AlexGyver/NixieClock_v2/case/IN-12_Max/Кнопки3.png

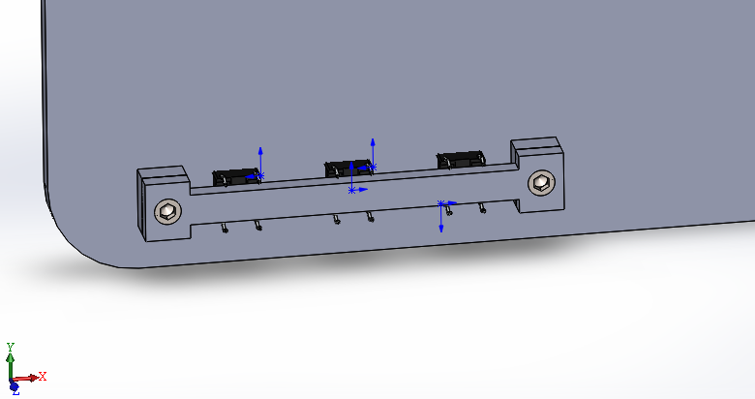
case/IN-12_Max/Кнопки3.png
