AlexGyver/NixieClock_v2/case/IN-12_Max/Крышка.png

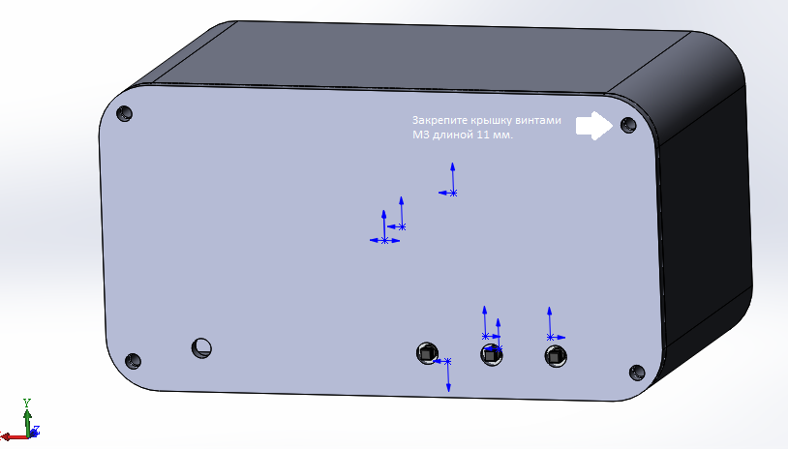
case/IN-12_Max/Крышка.png
