AlexGyver/NixieClock_v2/case/IN-12_Max/Панель.png

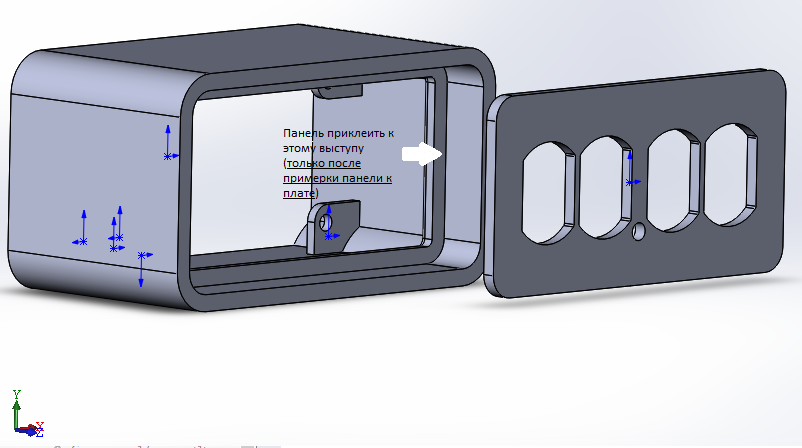
case/IN-12_Max/Панель.png
