AlexGyver/NixieClock_v2/case/IN-12_Max/Плата.png

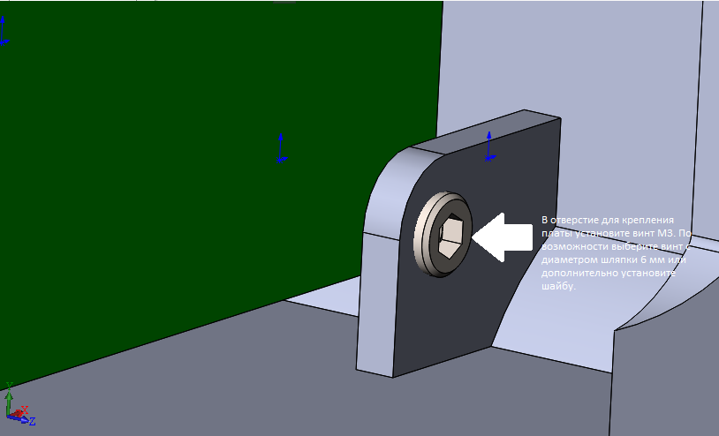
case/IN-12_Max/Плата.png
