AlexGyver/NixieClock_v2/case/IN-12_Max/Порядок сборки.png

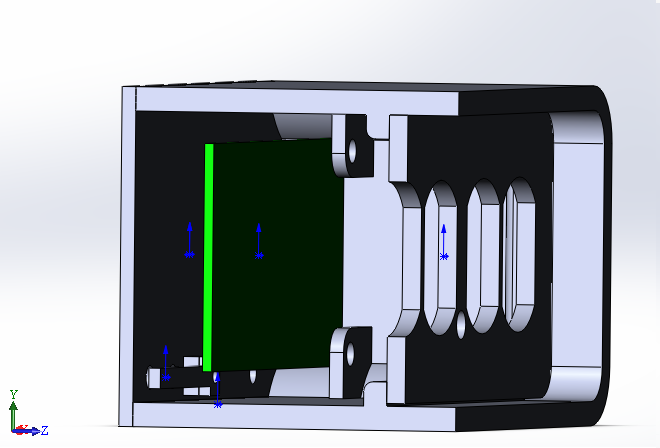
case/IN-12_Max/Порядок сборки.png
