AlexGyver/NixieClock_v2/case/IN-14_Gyver/fusion render.jpg

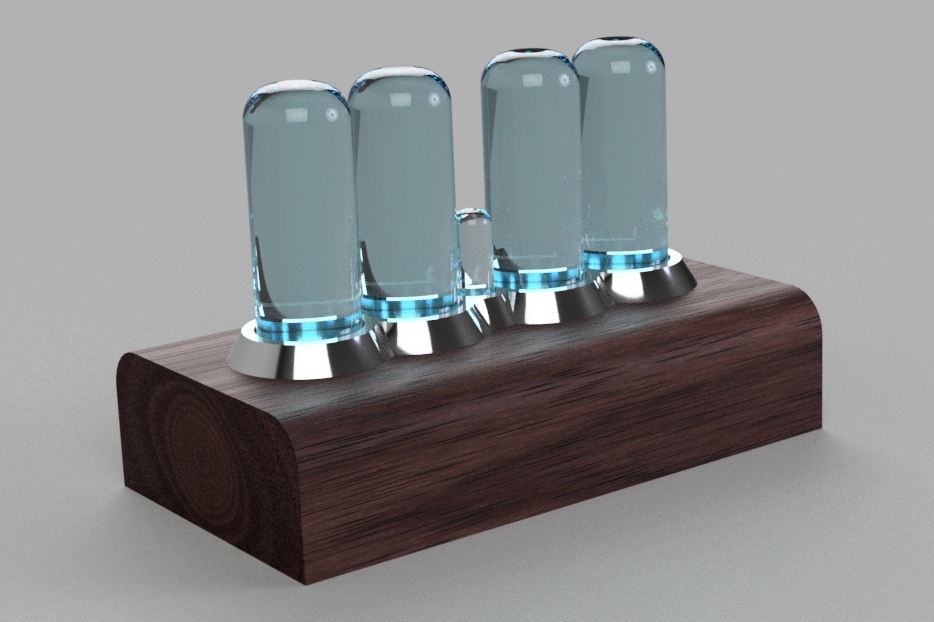
case/IN-14_Gyver/fusion render.jpg
