AlexGyver/NixieClock_v2/schemes/IN-12_norm.jpg

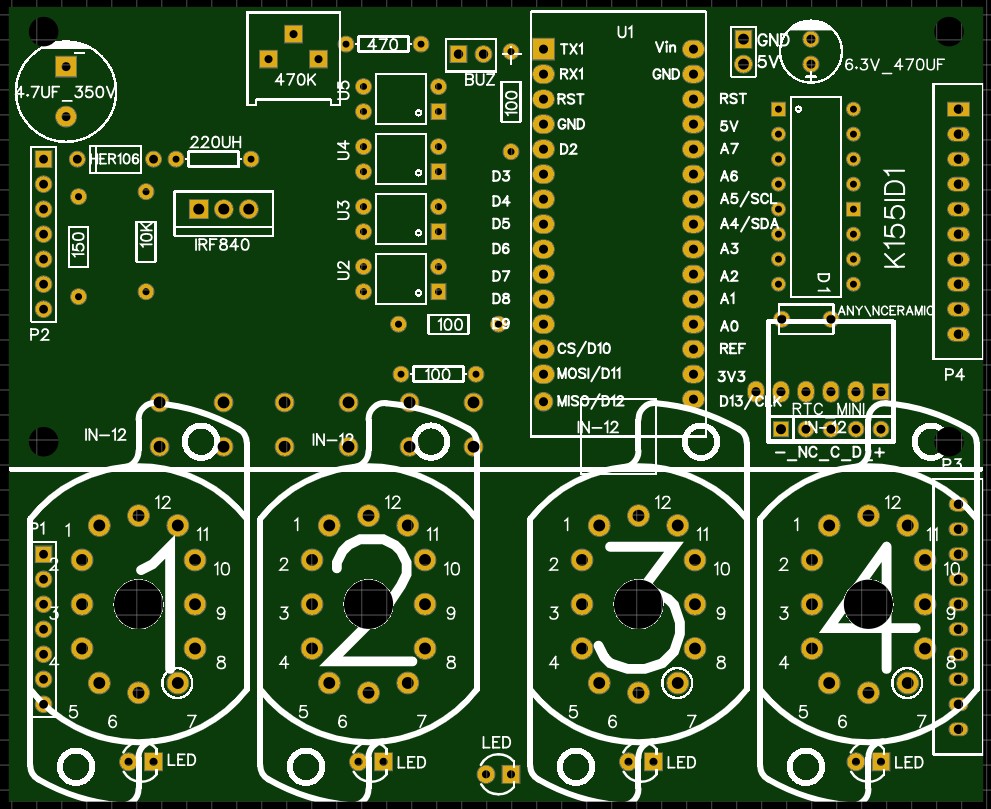
schemes/IN-12_norm.jpg
