AlexGyver/NixieClock_v2/schemes/lamp-check.jpg

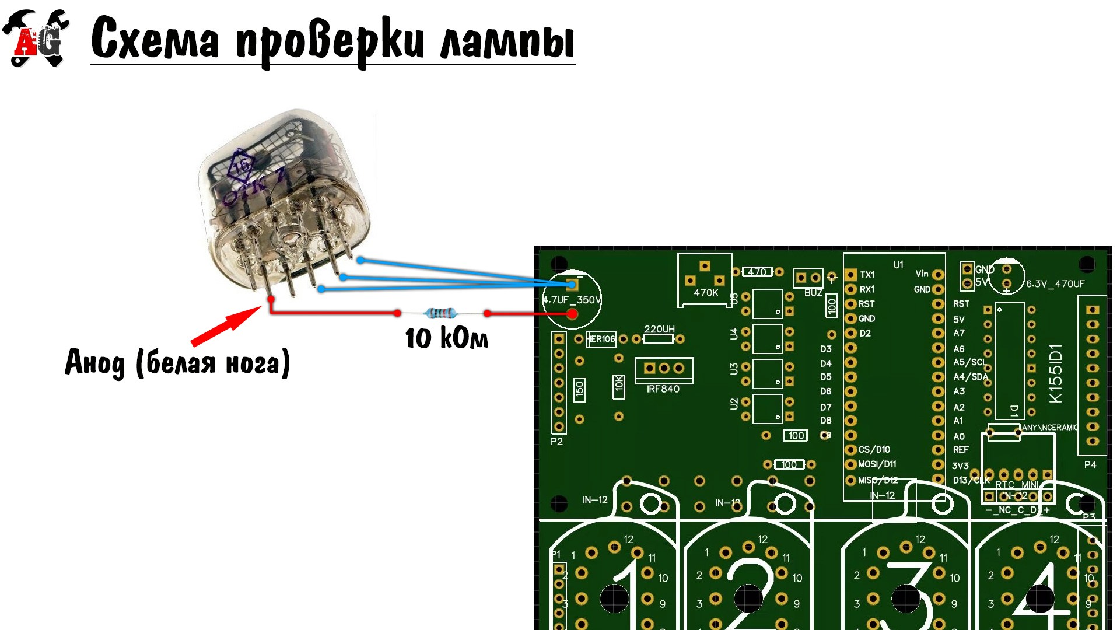
schemes/lamp-check.jpg
