AlexGyver/NixieClock_v2/schemes/pcbGuide3.jpg

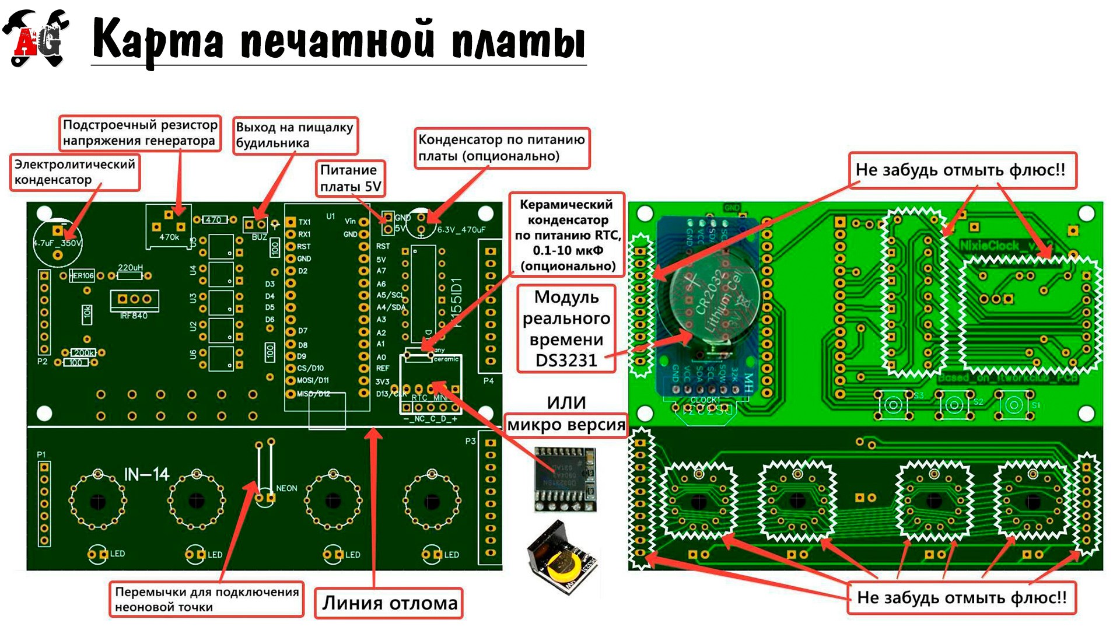
schemes/pcbGuide3.jpg
